mizma/flatbox/hardware-rev1.1/images/dmm-creators-market-header.jpg

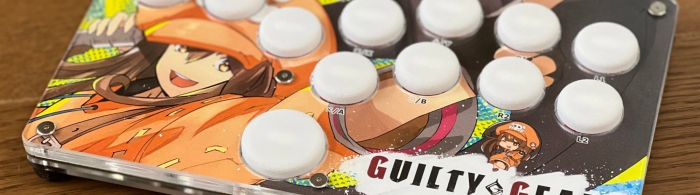
hardware-rev1.1/images/dmm-creators-market-header.jpg
