mizma/flatbox/hardware-rev1.1/images/Flatbox-ACR-Stencil_300dpi.png

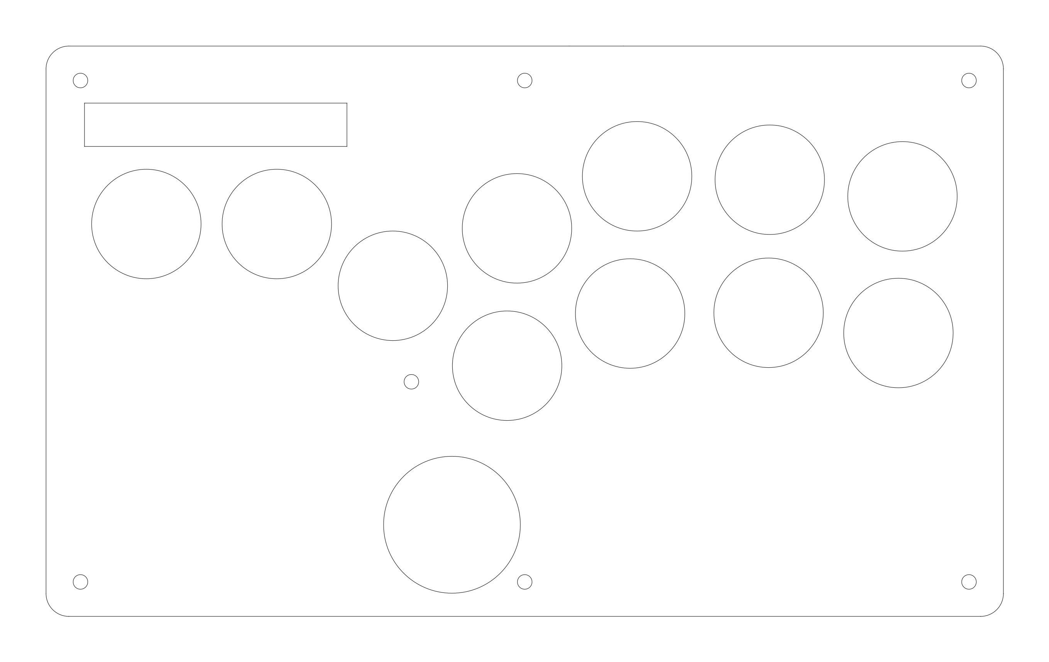
hardware-rev1.1/images/Flatbox-ACR-Stencil_300dpi.png
