mizma/flatbox/hardware-rev1.1/images/Flatbox-ACR-Stencil_with_key_label_300dpi.png

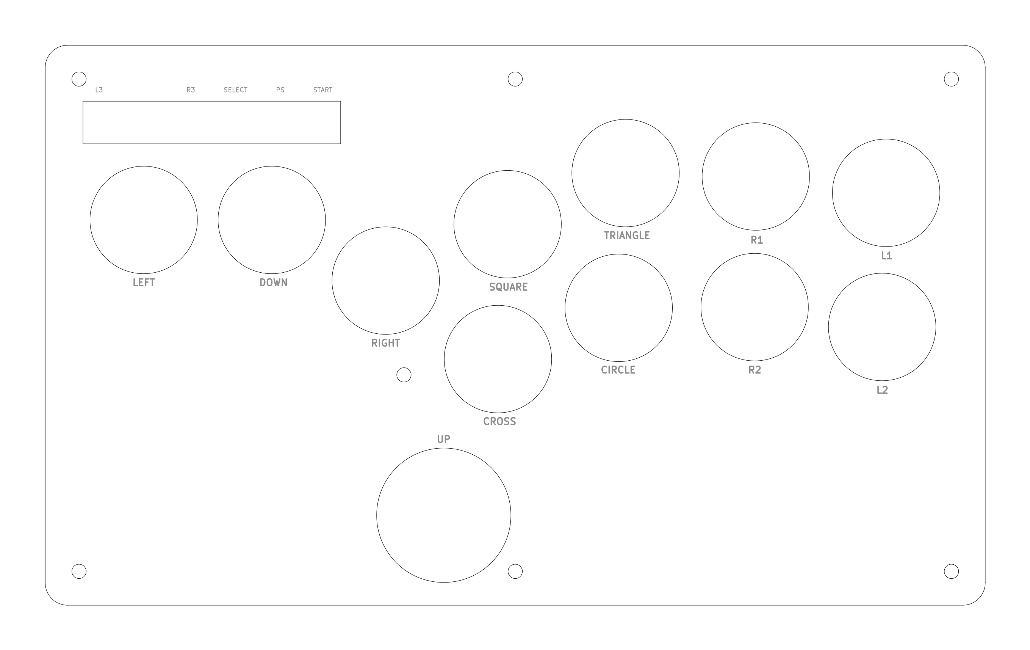
hardware-rev1.1/images/Flatbox-ACR-Stencil_with_key_label_300dpi.png
