mizma/flatbox/hardware-rev1.1/acrylic-shell/acryl-design-Flatbox-ACR-Acrylic-layer-03.dxf

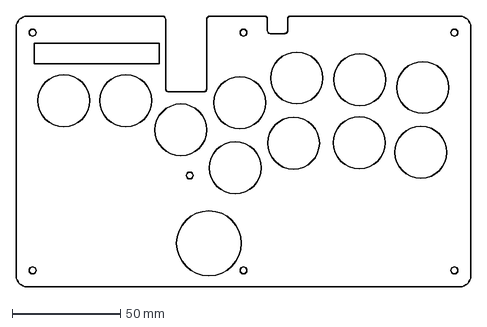
[picture p37: CAD file, 2022-07-22]
hardware-rev1.1/acrylic-shell/acryl-design-Flatbox-ACR-Acrylic-layer-03.dxf
210.0 x 125.0 mm
