mizma/flatbox/hardware-rev1.1/acrylic-shell/acryl-design-Flatbox-ACR-Acrylic-layer-05.dxf

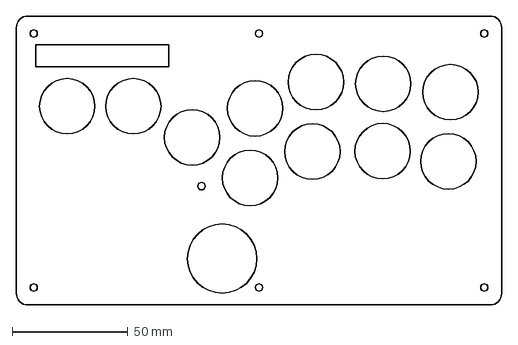
[picture p38: CAD file, 2022-07-22]
hardware-rev1.1/acrylic-shell/acryl-design-Flatbox-ACR-Acrylic-layer-05.dxf
210.0 x 125.0 mm
