mizma/flatbox/3d-printed-buttoncaps/Flatbox-ACR-ButtonCapBig.pdf

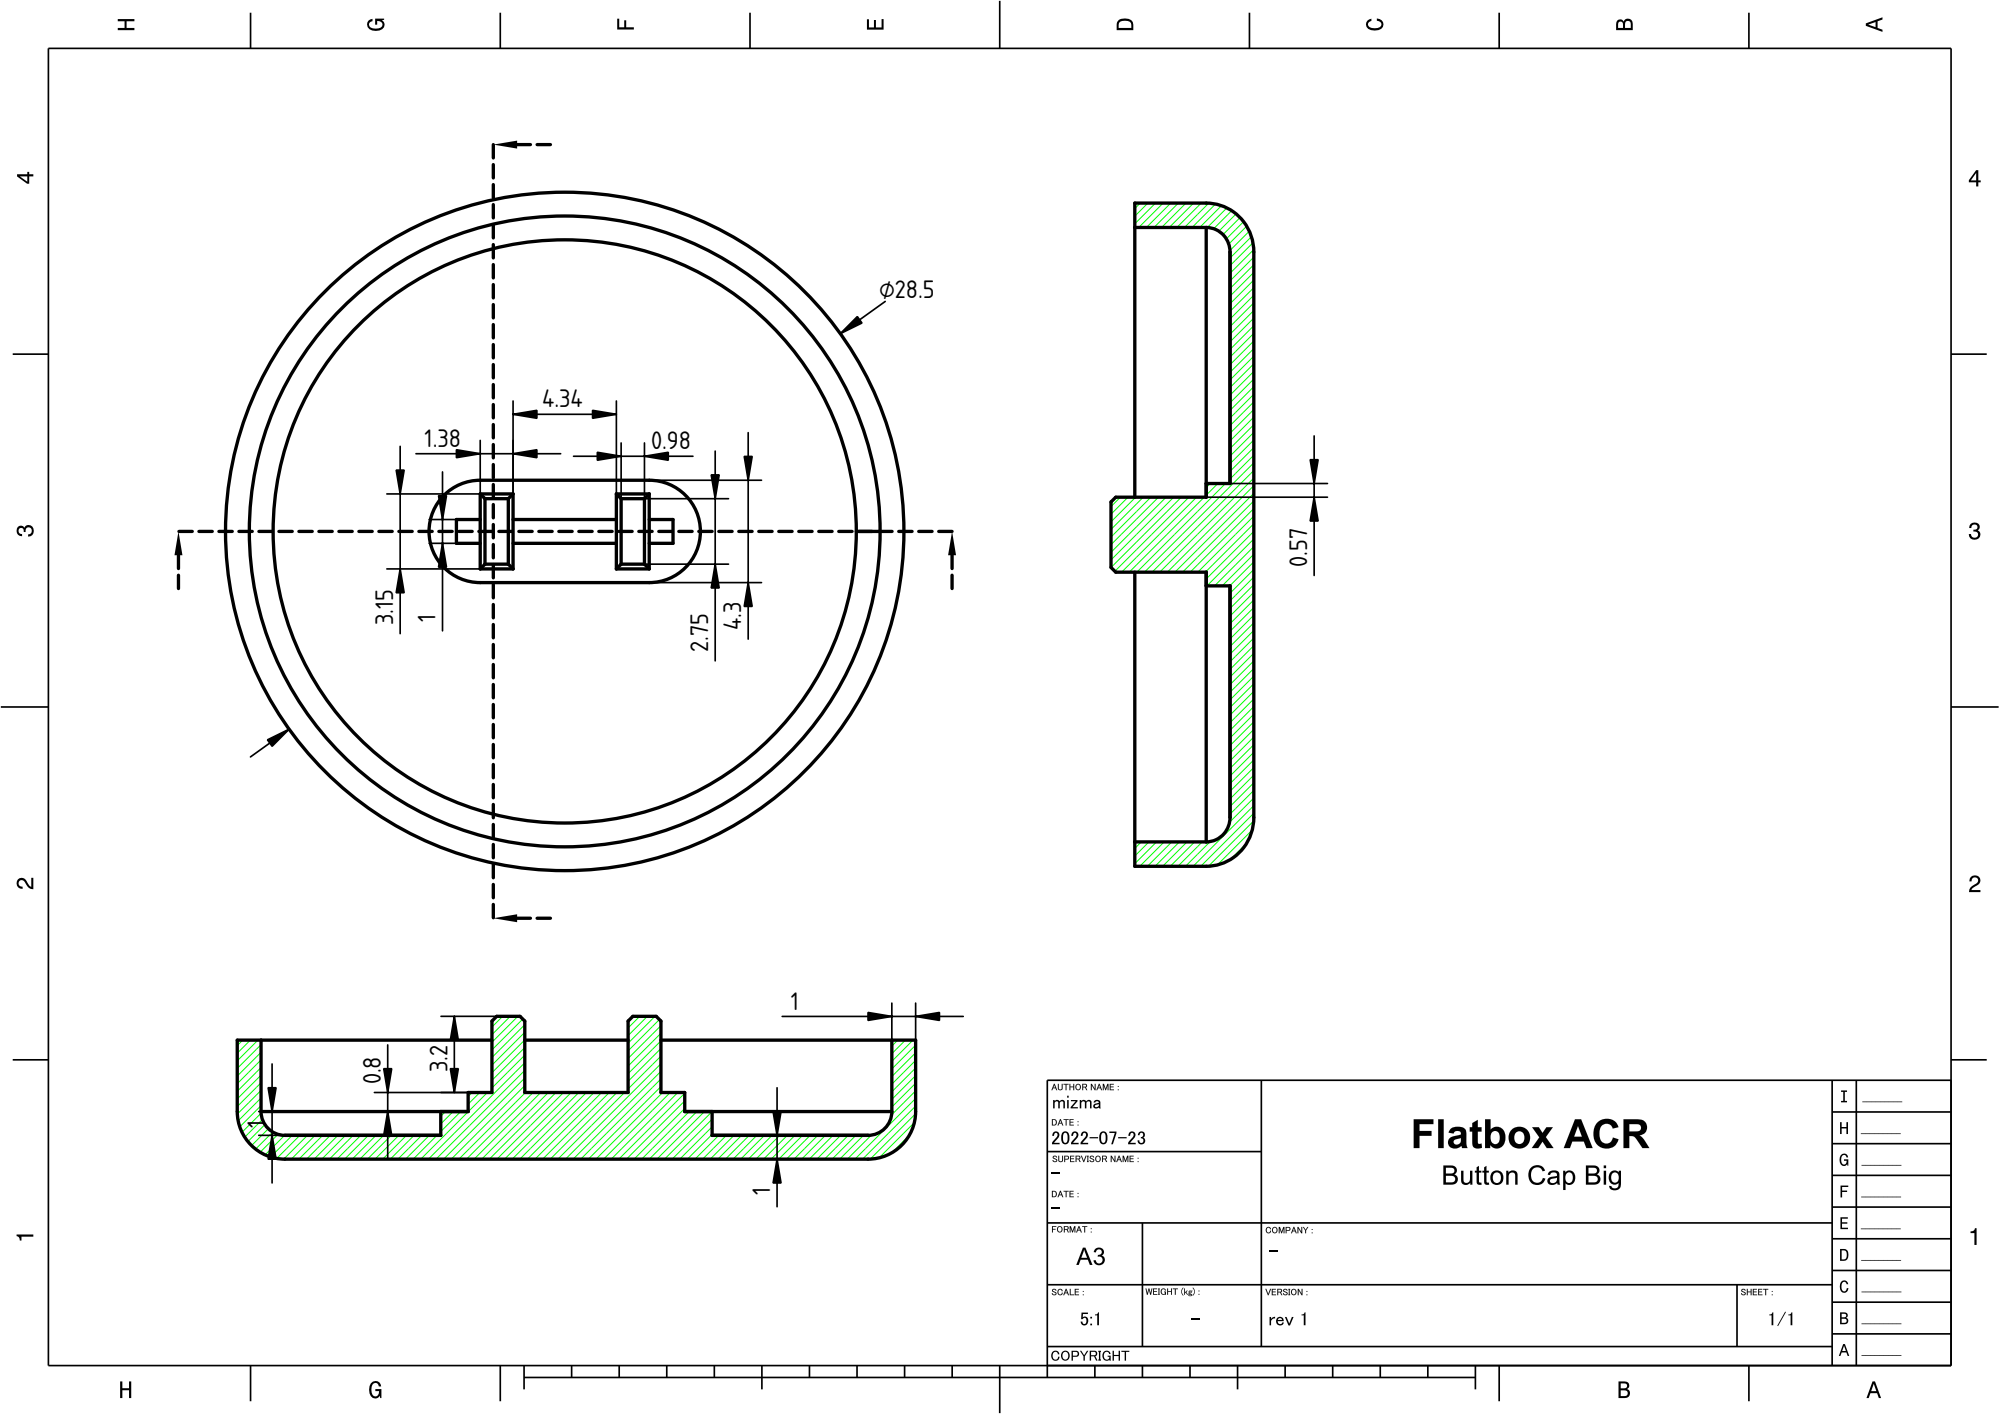
[picture p49: page 1]
